shabaz123/TMF8828/tmf8828_experiment_board/python/tmf8828_arduino_uno_file.csv

Tmf8828 Arduino Uno
#Conf | Period=264ms | KIter=500
# ... reset
#Obj | 65 | 0 | 18 | 18 | 388525 | 0 | 0 | 496 | 36 | 503 | 22 | 499 | 41 | 0 | 0 | 1051 | 14 | 0 | 0 | 2193 | 28 | 0 | 0 | 480 | 17 | 500 | 24 | 503 | 17 | 568 | 35 | 2405 | 19 | 808 | 16 | 0 | 0 | 2112 | 31 | 0 | 0 | 0 | 0 | 0 | 0 | 0 | 0 | 897 | 58 | 0 | 0 | 2031 | 60 | 0 | 0 | 0 | 0 | 0 | 0
#Obj | 65 | 1 | 18 | 19 | 767627 | 465 | 45 | 680 | 19 | 476 | 22 | 738 | 57 | 871 | 9 | 809 | 59 | 0 | 0 | 2063 | 20 | 0 | 0 | 461 | 52 | 0 | 0 | 450 | 52 | 729 | 51 | 866 | 16 | 809 | 42 | 2359 | 17 | 0 | 0 | 0 | 0 | 0 | 0 | 0 | 0 | 933 | 61 | 0 | 0 | 2230 | 44 | 1157 | 31 | 0 | 0 | 0 | 0 | 0 | 0
#Obj | 65 | 2 | 18 | 15 | 1153535 | 520 | 27 | 496 | 47 | 0 | 0 | 487 | 9 | 0 | 0 | 2092 | 50 | 0 | 0 | 0 | 0 | 0 | 0 | 505 | 26 | 517 | 43 | 919 | 52 | 775 | 73 | 2552 | 13 | 2036 | 48 | 0 | 0 | 0 | 0 | 0 | 0 | 856 | 13 | 786 | 41 | 0 | 0 | 917 | 73 | 0 | 0 | 0 | 0 | 0 | 0 | 0 | 0 | 0 | 0
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
