shabaz123/TMF8828/tmf8828_experiment_board/tmf8828_image.c

//


#include "tmf8828_image.h"
/*static*/ const unsigned long tmf8828_image_termination = 0x00200089;
/*static*/ const unsigned long tmf8828_image_start       = 0x00200000;
/*static*/ const unsigned long tmf8828_image_finish      = 0x00201BD8;
/*static*/ const unsigned long tmf8828_image_length      = 0x00001BD8;



/*static*/ const unsigned char tmf8828_image[7128] =
        {
                0x00, 0x80, 0x20, 0x00, 0x9D, 0x00, 0x20, 0x00, 0xD5, 0x20, 0x10, 0x00,
                0xD7, 0x20, 0x10, 0x00, 0x00, 0x00, 0x00, 0x00, 0x00, 0x00, 0x00, 0x00,
                0x00, 0x00, 0x00, 0x00, 0x00, 0x00, 0x00, 0x00, 0x00, 0x00, 0x00, 0x00,
                0x09, 0x12, 0x56, 0x34, 0xD8, 0x1B, 0x00, 0x00, 0xD9, 0x20, 0x10, 0x00,
                0x00, 0x00, 0x00, 0x00, 0x00, 0x00, 0x00, 0x00, 0xDB, 0x20, 0x10, 0x00,
                0xDD, 0x20, 0x10, 0x00, 0xDF, 0x20, 0x10, 0x00, 0x39, 0x01, 0x20, 0x00,
                0x61, 0x23, 0x10, 0x00, 0xDF, 0x20, 0x10, 0x00, 0x85, 0x22, 0x10, 0x00,
                0x99, 0x22, 0x10, 0x00, 0xDF, 0x20, 0x10, 0x00, 0xDF, 0x20, 0x10, 0x00,
                0xDF, 0x20, 0x10, 0x00, 0x51, 0x23, 0x10, 0x00, 0xE1, 0x20, 0x10, 0x00,
                0xE1, 0x20, 0x10, 0x00, 0x05, 0x24, 0x10, 0x00, 0x2D, 0x24, 0x10, 0x00,
                0x4D, 0x24, 0x10, 0x00, 0xDF, 0x20, 0x10, 0x00, 0xDF, 0x20, 0x10, 0x00,
                0x53, 0x29, 0xCD, 0x68, 0x03, 0x48, 0x85, 0x46, 0x00, 0xF0, 0x16, 0xF8,
                0x00, 0x48, 0x00, 0x47, 0xE1, 0x00, 0x20, 0x00, 0x00, 0x80, 0x20, 0x00,
                0x05, 0x48, 0x80, 0x47, 0x05, 0x48, 0x00, 0x47, 0xFE, 0xE7, 0xFE, 0xE7,
                0xFE, 0xE7, 0xFE, 0xE7, 0x70, 0x47, 0xFE, 0xE7, 0x70, 0x47, 0x00, 0x00,
                0xED, 0x6D, 0x10, 0x00, 0x89, 0x00, 0x20, 0x00, 0x06, 0x4C, 0x01, 0x25,
                0x06, 0x4E, 0x05, 0xE0, 0xE3, 0x68, 0x07, 0xCC, 0x2B, 0x43, 0x0C, 0x3C,
                0x98, 0x47, 0x10, 0x34, 0xB4, 0x42, 0xF7, 0xD3, 0xFF, 0xF7, 0xDC, 0xFF,
                0xD8, 0x1B, 0x20, 0x00, 0xD8, 0x1B, 0x20, 0x00, 0x13, 0x48, 0x02, 0xF7,
                0xD3, 0xFD, 0x13, 0x4C, 0x05, 0x46, 0x01, 0x28, 0x01, 0xD1, 0x08, 0x20,
                0x60, 0x62, 0x0E, 0x20, 0x00, 0xF7, 0x38, 0xFA, 0x61, 0x6A, 0x08, 0x29,
                0x04, 0xD1, 0x80, 0x09, 0x03, 0x28, 0x01, 0xD0, 0x00, 0x20, 0x60, 0x62,
                0xA0, 0x8C, 0x10, 0x21, 0xC0, 0xB2, 0x04, 0xF7, 0xF5, 0xFE, 0x60, 0x6A,
                0x08, 0x28, 0x28, 0x46, 0x06, 0xD0, 0x00, 0xF0, 0x1F, 0xFB, 0x6F, 0x20,
                0x01, 0xF0, 0x56, 0xF8, 0x00, 0xF0, 0x60, 0xFB, 0x00, 0xF0, 0xFE, 0xFD,
                0x00, 0xF0, 0x5E, 0xFE, 0xA8, 0x80, 0x10, 0x00, 0xD8, 0x1B, 0x20, 0x00,
                0x70, 0xB5, 0x15, 0x4E, 0x35, 0x6B, 0x15, 0x4C, 0xA8, 0x07, 0x06, 0xD5,
                0x01, 0xF7, 0xE6, 0xF8, 0x20, 0x30, 0x06, 0xF7, 0x90, 0xFA, 0xFF, 0x28,
                0x0F, 0xD0, 0x02, 0xF7, 0xAB, 0xF8, 0x21, 0x78, 0x0F, 0x48, 0x6C, 0x29,
                0x15, 0xD0, 0x21, 0x78, 0x65, 0x29, 0x05, 0xD1, 0x00, 0x21, 0x41, 0x62,
                0x01, 0xF7, 0x86, 0xFC, 0x01, 0xF7, 0x10, 0xFD, 0x70, 0xBD, 0x20, 0x70,
                0x09, 0x48, 0x80, 0x68, 0x80, 0x47, 0x09, 0x48, 0x81, 0x79, 0x06, 0x22,
                0x11, 0x43, 0x81, 0x71, 0x35, 0x63, 0x40, 0xBF, 0x70, 0xBD, 0x08, 0x21,
                0xEB, 0xE7, 0x00, 0x00, 0x00, 0x10, 0x01, 0x40, 0x39, 0x45, 0x20, 0x00,
                0xD8, 0x1B, 0x20, 0x00, 0x38, 0x3C, 0x20, 0x00, 0xBC, 0x3C, 0x20, 0x00,
                0x70, 0xB5, 0x16, 0x46, 0x0C, 0x46, 0x00, 0xF0, 0xBD, 0xFF, 0x6E, 0x28,
                0x2E, 0xD0, 0x18, 0x4D, 0x80, 0x34, 0x28, 0x46, 0x21, 0x6B, 0x02, 0xF7,
                0x6F, 0xF9, 0x49, 0x04, 0xC0, 0x0B, 0x08, 0x43, 0x14, 0x4C, 0x00, 0x2E,
                0x60, 0x62, 0x08, 0xD0, 0x80, 0x36, 0x28, 0x46, 0x31, 0x6B, 0x02, 0xF7,
                0x63, 0xF9, 0x49, 0x04, 0xC0, 0x0B, 0x08, 0x43, 0xA0, 0x62, 0x01, 0x20,
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
        };
