shabaz123/TMF8828/tmf8828_experiment_board/tmf8828_calib.c

//


#include "tmf8828_calib.h"
#include "common_utils.h"

const uint8_t tmf8828_calib_0[192] = {
        0x19, 0x3, 0xBC, 0x0, 0x1, 0x4, 0x1, 0x1,
        0x1, 0x1, 0xA0, 0xF, 0x87, 0x56, 0x34, 0x12,
        0xC3, 0x8A, 0x4D, 0x31, 0xD7, 0x5D, 0x7, 0x0,
        0x35, 0x3F, 0x7, 0x0, 0x97, 0x6D, 0x7, 0x0,
        0x14, 0x67, 0x7, 0x0, 0xDD, 0x54, 0x7, 0x0,
        0x48, 0x58, 0x7, 0x0, 0x5C, 0x77, 0x7, 0x0,
        0x45, 0x74, 0x7, 0x0, 0x45, 0x74, 0x7, 0x0,
        0xD7, 0x5D, 0x7, 0x0, 0xF, 0xFC, 0x5, 0x0,
        0x58, 0x5E, 0x0, 0x0, 0x92, 0x60, 0x0, 0x0,
        0xE1, 0x77, 0x0, 0x0, 0xE2, 0x41, 0x0, 0x0,
        0xA3, 0x1F, 0x1, 0x0, 0xC1, 0x47, 0x0, 0x0,
        0x5D, 0x9B, 0x0, 0x0, 0x14, 0x42, 0x0, 0x0,
        0x1, 0x0, 0x0, 0x0, 0x87, 0x56, 0x34, 0x12,
        0xBB, 0xE4, 0xE6, 0x81, 0xBC, 0x5C, 0x7, 0x0,
        0x73, 0x40, 0x7, 0x0, 0xF4, 0x69, 0x7, 0x0,
        0x14, 0x67, 0x7, 0x0, 0x87, 0x52, 0x7, 0x0,
        0xB2, 0x53, 0x7, 0x0, 0xA4, 0x72, 0x7, 0x0,
        0x5C, 0x77, 0x7, 0x0, 0xD3, 0x71, 0x7, 0x0,
        0xBC, 0x5C, 0x7, 0x0, 0x71, 0xE4, 0x5, 0x0,
        0x50, 0x4F, 0x0, 0x0, 0x3F, 0x73, 0x0, 0x0,
        0x70, 0x59, 0x0, 0x0, 0x36, 0x43, 0x0, 0x0,
        0xD, 0x98, 0x0, 0x0, 0x9E, 0x46, 0x0, 0x0,
        0x1F, 0x68, 0x0, 0x0, 0xA4, 0x48, 0x0, 0x0,
        0x1, 0x0, 0x0, 0x0, 0x0, 0x0, 0xFC, 0x7D,
};

const uint8_t tmf8828_calib_1[192] = {
        0x19, 0x4, 0xBC, 0x0, 0x1, 0x4, 0x1, 0x1,
        0x1, 0x1, 0xA0, 0xF, 0x87, 0x56, 0x34, 0x12,
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
        0x84, 0x4A, 0x0, 0x0, 0x16, 0x9D, 0x0, 0x0,
        0x25, 0x4E, 0x0, 0x0, 0xF4, 0x5D, 0x0, 0x0,
        0x7F, 0x4B, 0x0, 0x0, 0x4, 0x5D, 0x0, 0x0,
        0x9C, 0x4C, 0x0, 0x0, 0x4, 0x91, 0x0, 0x0,
        0x1, 0x0, 0x0, 0x0, 0x0, 0x0, 0xFE, 0x7E,
};
