shabaz123/TMF8828/tmf8828_experiment_board/tmf8828_calib.h

//

#ifndef TMF8828_EXPERIMENT_BOARD_TMF8828_CALIB_H
#define TMF8828_EXPERIMENT_BOARD_TMF8828_CALIB_H

#include "pico/stdlib.h"
#include "fsp_error.h"



#endif //TMF8828_EXPERIMENT_BOARD_TMF8828_CALIB_H
