shabaz123/TMF8828/tmf8828_experiment_board/tmf8828_image.h

//


#ifndef TMF8828_EXPERIMENT_BOARD_TMF8828_IMAGE_H
#define TMF8828_EXPERIMENT_BOARD_TMF8828_IMAGE_H

#include "pico/stdlib.h"
#include "fsp_error.h"

#define TMF8828_IMAGE_TERMINATION 0x00200089
#define TMF8828_IMAGE_START       0x00200000
#define TMF8828_IMAGE_FINISH      0x00201BD8
#define TMF8828_IMAGE_LENGTH      0x00001BD8


#endif //TMF8828_EXPERIMENT_BOARD_TMF8828_IMAGE_H
